tuanthanhhh/trek-safety-system/Firmware_TRILE/Firmware/Core/Peripheral/SH1160/bitmap.h

/*
 * bitmap.h
 *
 *  Created on: 17-Jun-2019
 *      Author: poe
 */

#ifndef BITMAP_H_
#define BITMAP_H_

#define SELECT_FRAME_WIDTH		125
#define	SELECT_FRAME_HEIGHT		21



extern const unsigned char logo [];
extern const unsigned char LOGO_BW_map[];
extern const unsigned char selected_frame[];
extern const unsigned char icon_compass[];
extern const unsigned char icon_settings[];
extern const unsigned char icon_GPS[];
extern const unsigned char Compass[];
extern const unsigned char GPS[];
extern const unsigned char Settings[];
extern const unsigned char icon_battery[];
extern const unsigned char pin_cell[];


#endif /* BITMAP_H_ */
